loglow/TrueUp-Glide-Mod/STL/PSU Mount.stl

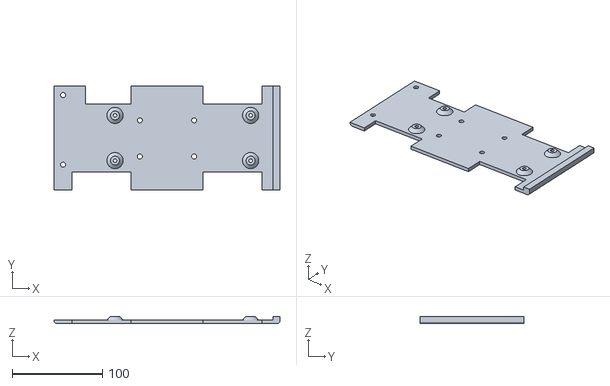
[picture p16: CAD file, 2017-04-15]
STL/PSU Mount.stl
250.0 x 115.0 x 8.00
