loglow/TrueUp-Glide-Mod/STL/Frame Foot.stl

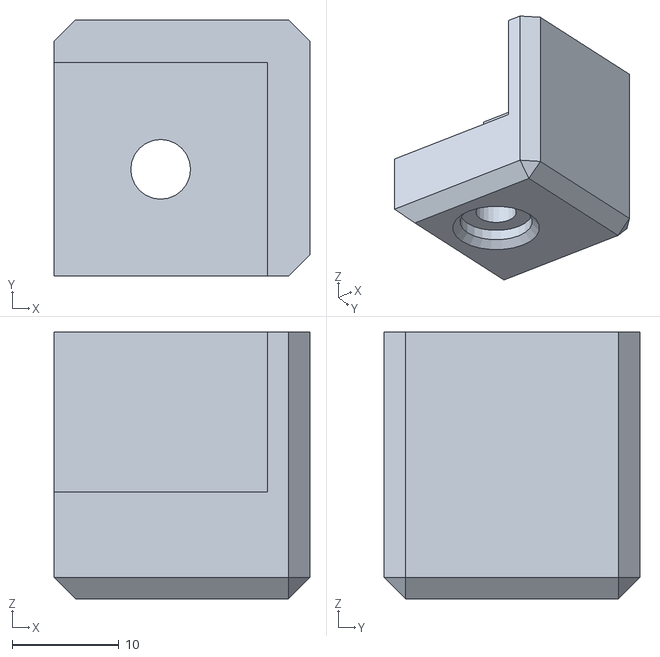
[picture p17: CAD file, 2017-04-15]
STL/Frame Foot.stl
24.0 x 24.0 x 25.0
