loglow/TrueUp-Glide-Mod/STL/MKS Mount.stl

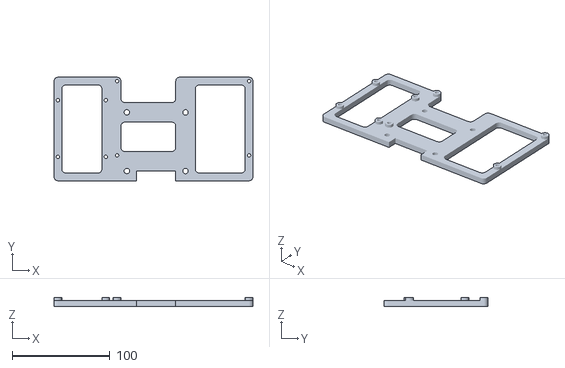
[picture p18: CAD file, 2017-04-15]
STL/MKS Mount.stl
203.5 x 106.0 x 9.00
