loglow/TrueUp-Glide-Mod/STL/Y Belt Keeper Spacer.stl

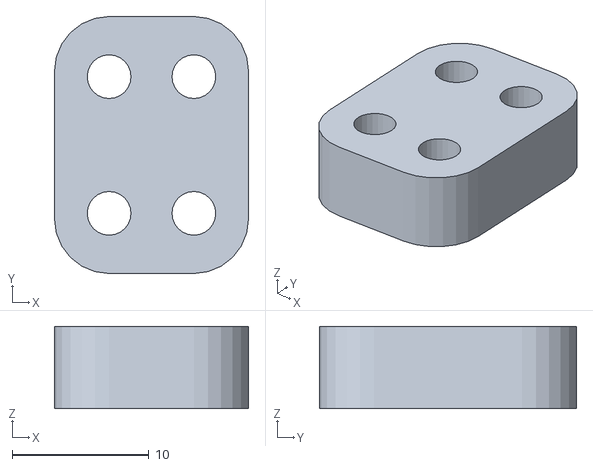
[picture p19: CAD file, 2017-04-15]
STL/Y Belt Keeper Spacer.stl
14.2 x 18.8 x 6.00
