loglow/TrueUp-Glide-Mod/STL/Z Glide Body, Left.stl

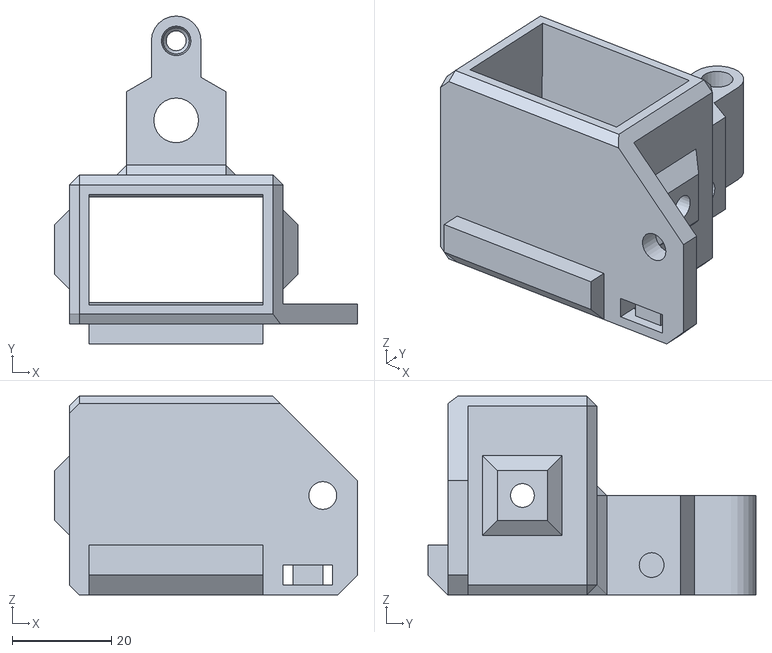
[picture p20: CAD file, 2017-04-15]
STL/Z Glide Body, Left.stl
61.0 x 66.0 x 40.0
