loglow/TrueUp-Glide-Mod/STL/Y Idler Bracket.stl

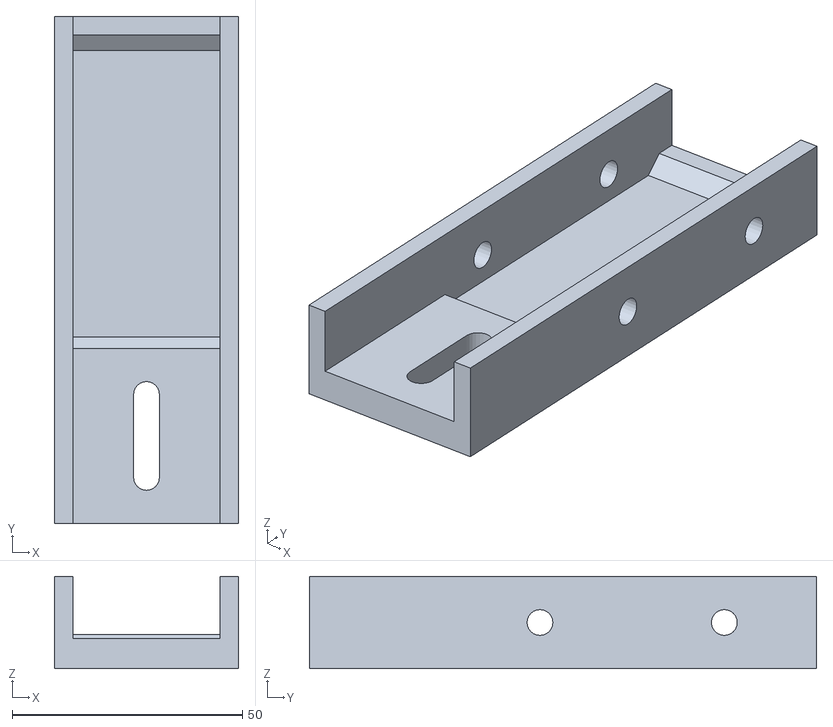
[picture p21: CAD file, 2017-04-15]
STL/Y Idler Bracket.stl
40.0 x 110.0 x 20.0
