loglow/TrueUp-Glide-Mod/STL/Y Belt Keeper Teeth.stl

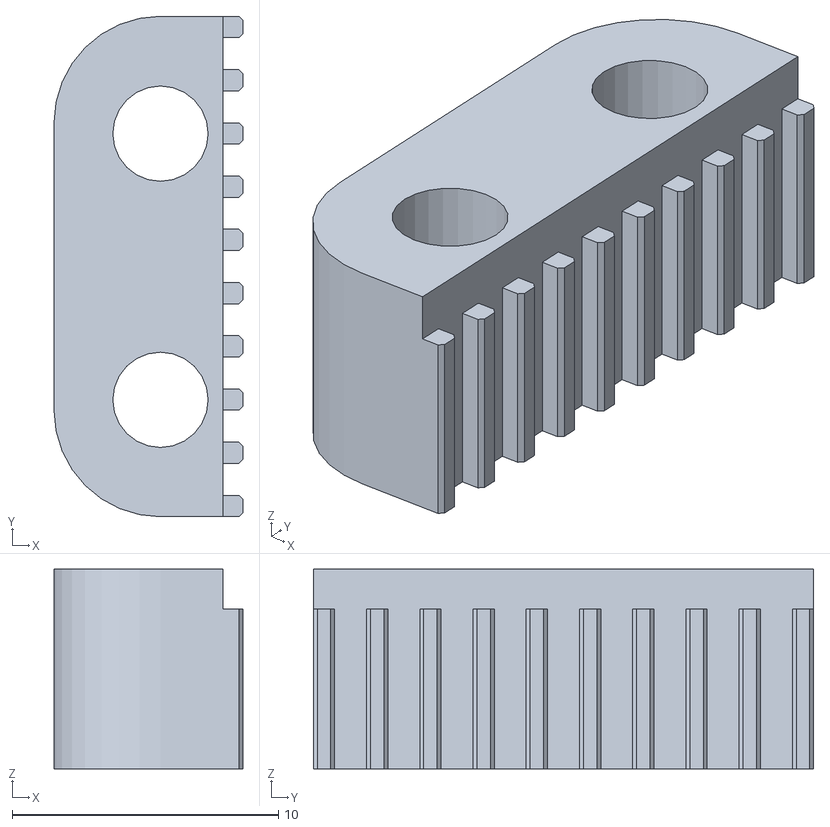
[picture p22: CAD file, 2017-04-15]
STL/Y Belt Keeper Teeth.stl
7.10 x 18.8 x 7.50
