loglow/TrueUp-Glide-Mod/STL/Handle.stl

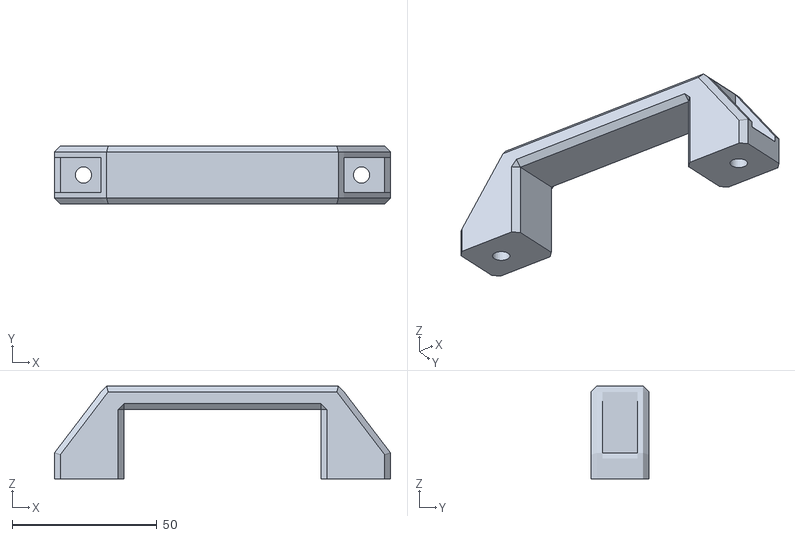
[picture p23: CAD file, 2017-04-15]
STL/Handle.stl
116.0 x 20.0 x 32.0
