loglow/TrueUp-Glide-Mod/STL/Control Box, Left.stl

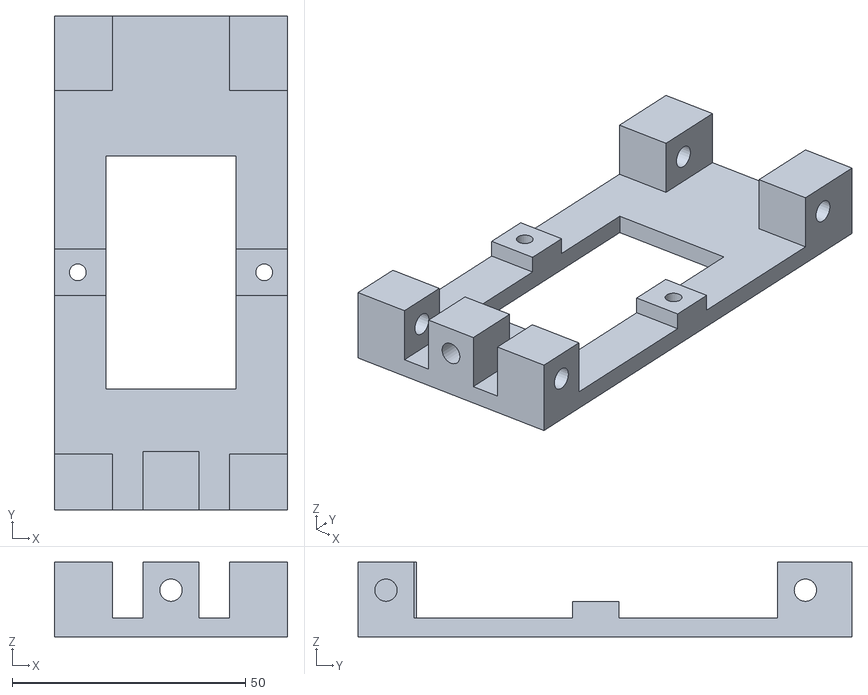
[picture p24: CAD file, 2017-04-15]
STL/Control Box, Left.stl
50.0 x 106.0 x 16.0
