loglow/TrueUp-Glide-Mod/STL/Y Mount Bracket.stl

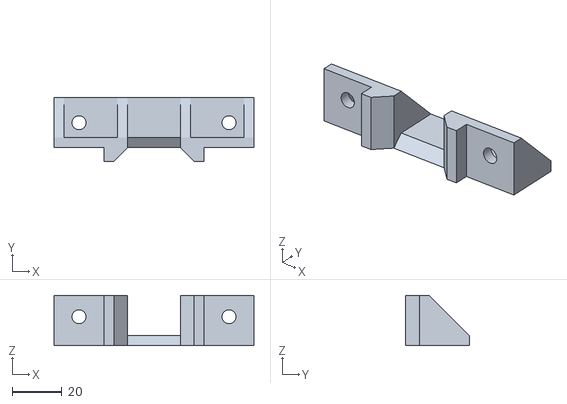
[picture p25: CAD file, 2017-04-15]
STL/Y Mount Bracket.stl
80.0 x 25.4 x 20.0
