loglow/TrueUp-Glide-Mod/STL/Y Belt Keeper Flat.stl

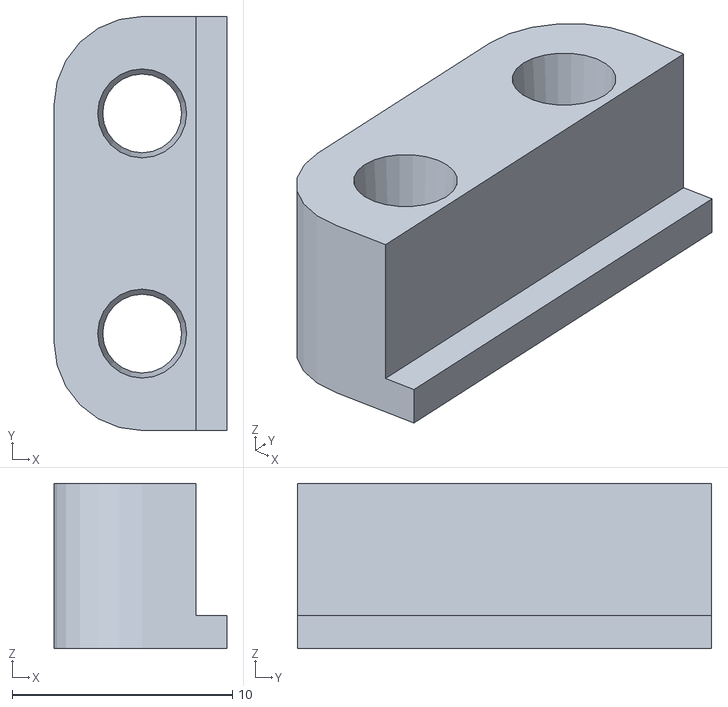
[picture p26: CAD file, 2017-04-15]
STL/Y Belt Keeper Flat.stl
7.85 x 18.8 x 7.50
