loglow/TrueUp-Glide-Mod/STL/Spool Mount.stl

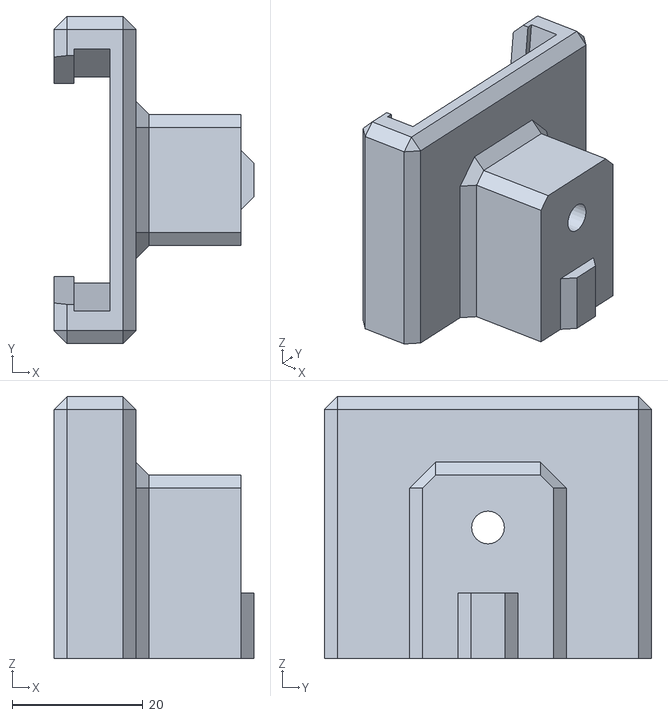
[picture p27: CAD file, 2017-04-15]
STL/Spool Mount.stl
30.5 x 50.0 x 40.0
