loglow/TrueUp-Glide-Mod/STL/Control Box, Bottom.stl

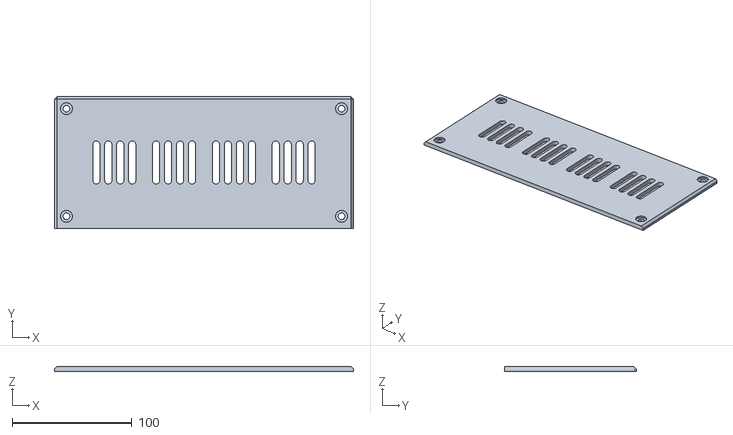
[picture p28: CAD file, 2017-04-15]
STL/Control Box, Bottom.stl
250.0 x 110.0 x 4.00
