loglow/TrueUp-Glide-Mod/STL/Top Corner, Left.stl

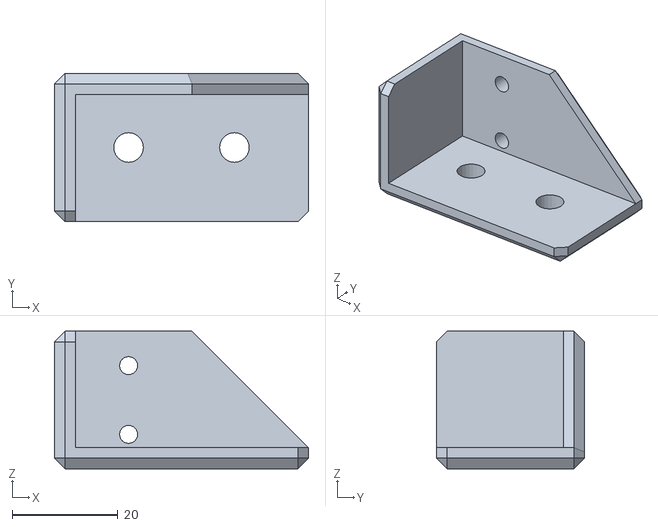
[picture p29: CAD file, 2017-04-15]
STL/Top Corner, Left.stl
48.0 x 28.0 x 26.0
