loglow/TrueUp-Glide-Mod/STL/Crossover Cover.stl

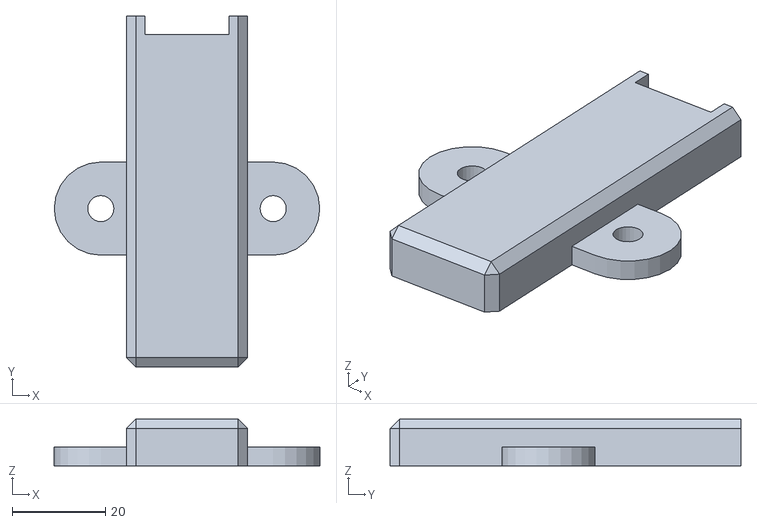
[picture p30: CAD file, 2017-04-15]
STL/Crossover Cover.stl
57.0 x 75.4 x 10.0
