loglow/TrueUp-Glide-Mod/STL/Z Endstop Bracket.stl

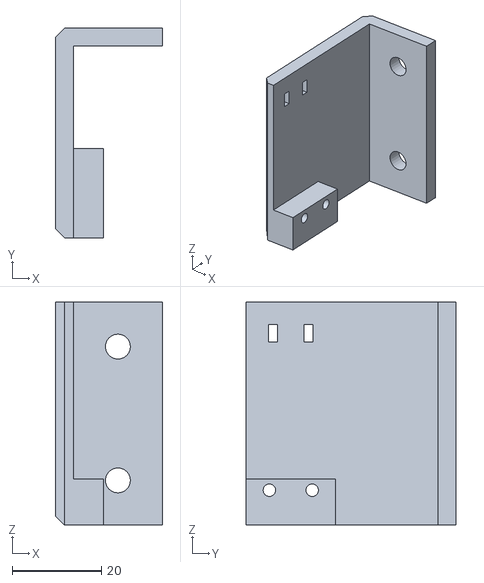
[picture p31: CAD file, 2017-04-15]
STL/Z Endstop Bracket.stl
24.0 x 47.0 x 50.0
