loglow/TrueUp-Glide-Mod/STL/X Motor Mount.stl

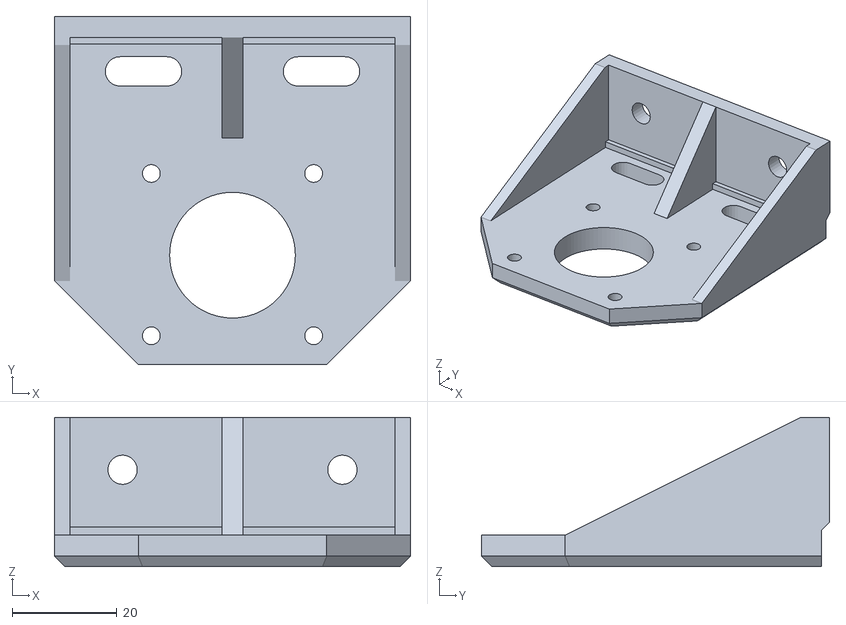
[picture p32: CAD file, 2017-04-15]
STL/X Motor Mount.stl
68.0 x 66.5 x 28.5
