loglow/TrueUp-Glide-Mod/STL/Print Fan Nozzle.stl

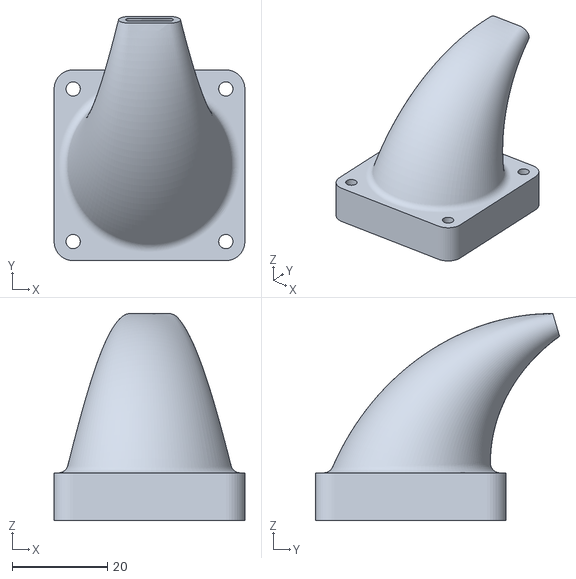
[picture p33: CAD file, 2017-04-15]
STL/Print Fan Nozzle.stl
40.0 x 51.2 x 43.4
