loglow/TrueUp-Glide-Mod/STL/Front Foot.stl

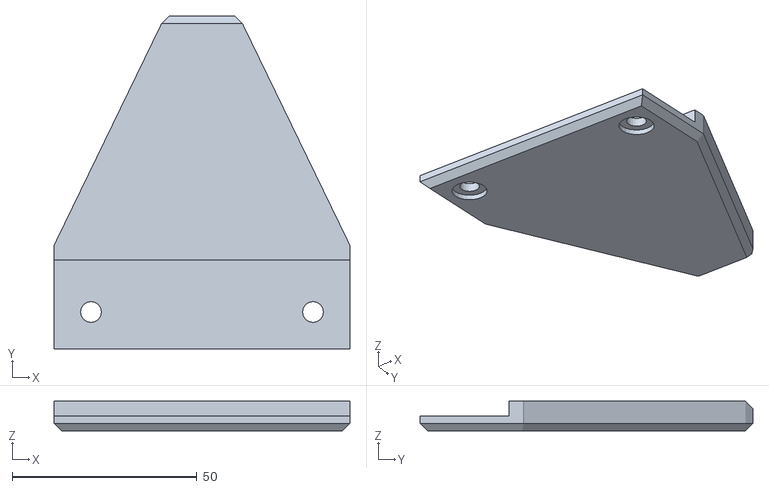
[picture p34: CAD file, 2017-04-15]
STL/Front Foot.stl
80.0 x 90.0 x 8.00
