loglow/TrueUp-Glide-Mod/STL/PSU Top.stl

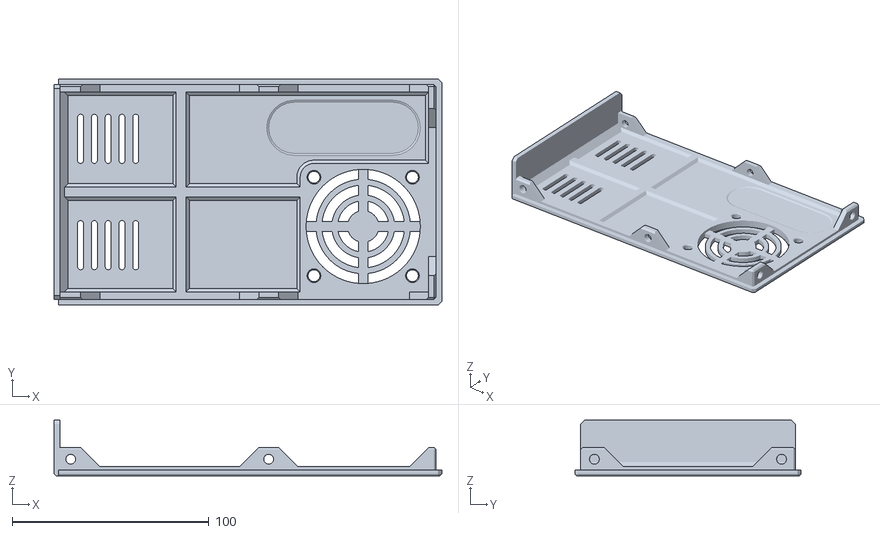
[picture p35: CAD file, 2017-04-15]
STL/PSU Top.stl
197.0 x 115.0 x 28.4
