loglow/TrueUp-Glide-Mod/STL/Control Box Fan Mount.stl

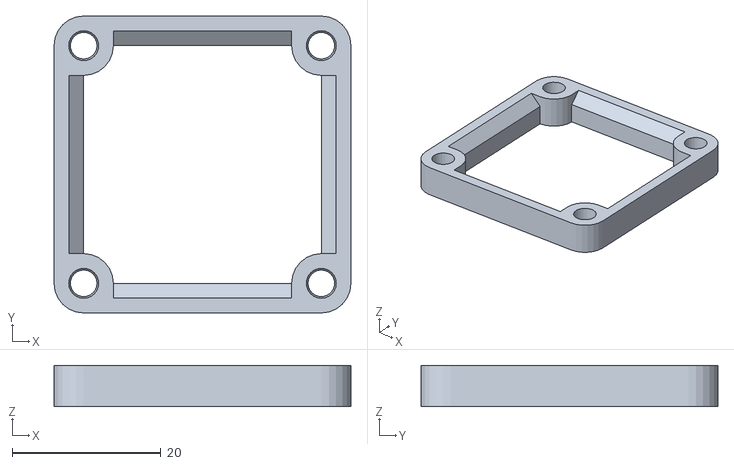
[picture p36: CAD file, 2017-04-15]
STL/Control Box Fan Mount.stl
40.0 x 40.0 x 5.56
