loglow/TrueUp-Glide-Mod/STL/Control Box, Front.stl

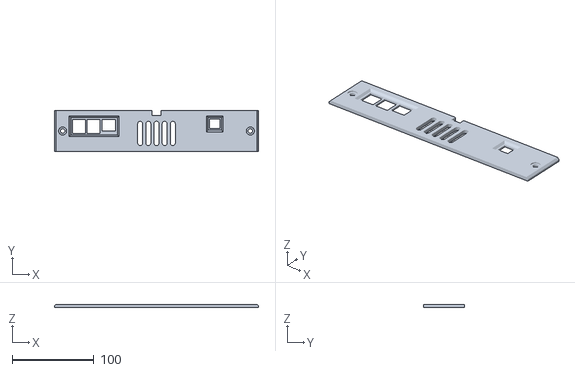
[picture p37: CAD file, 2017-04-15]
STL/Control Box, Front.stl
250.0 x 50.0 x 4.00
