loglow/TrueUp-Glide-Mod/STL/Z Bearing Mount.stl

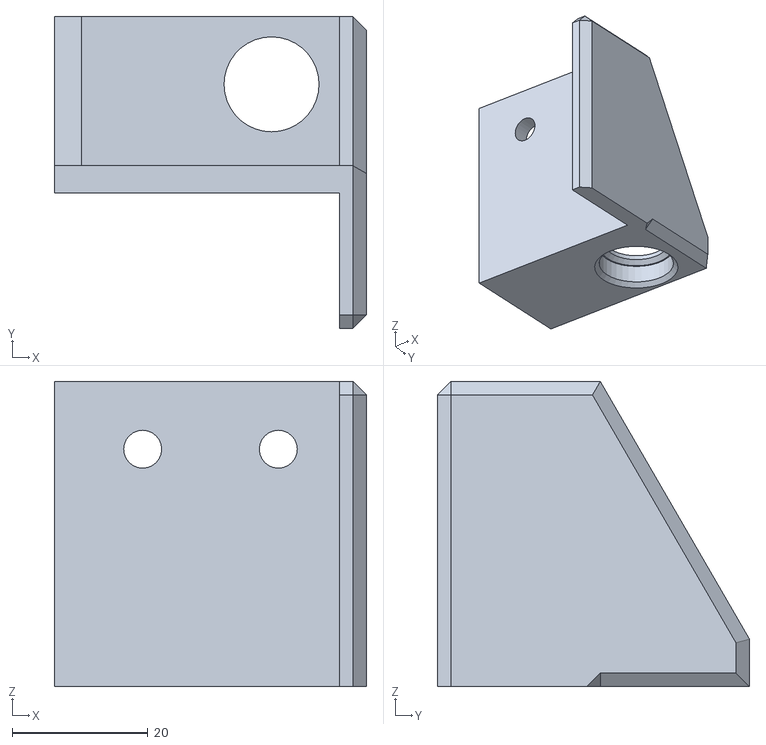
[picture p38: CAD file, 2017-04-15]
STL/Z Bearing Mount.stl
46.0 x 46.0 x 45.0
