loglow/TrueUp-Glide-Mod/STL/Spool Holder.stl

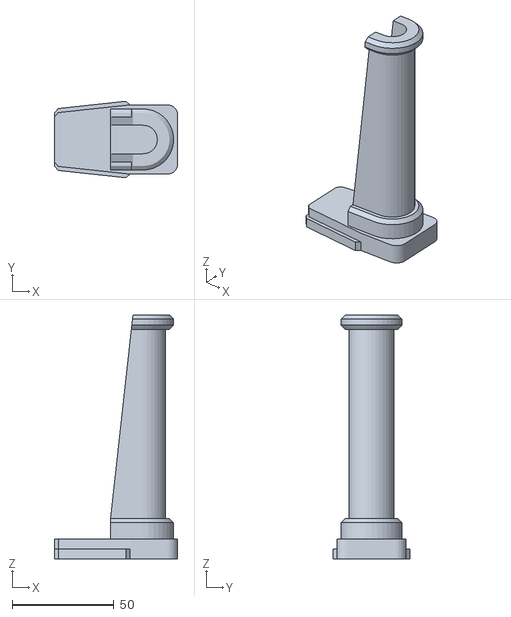
[picture p39: CAD file, 2017-04-15]
STL/Spool Holder.stl
60.6 x 37.6 x 119.8
