loglow/TrueUp-Glide-Mod/STL/X Leveling Jig.stl

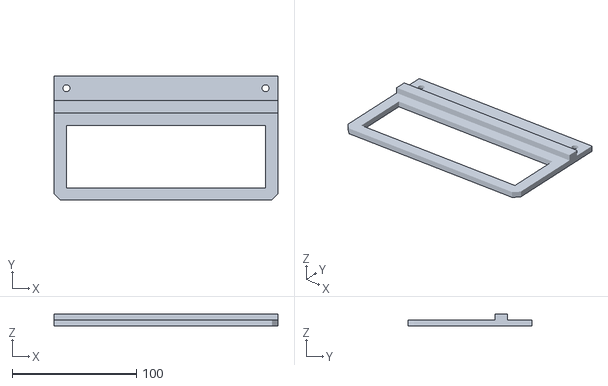
[picture p40: CAD file, 2017-04-15]
STL/X Leveling Jig.stl
180.0 x 100.0 x 10.0
