loglow/TrueUp-Glide-Mod/STL/Y Center.stl

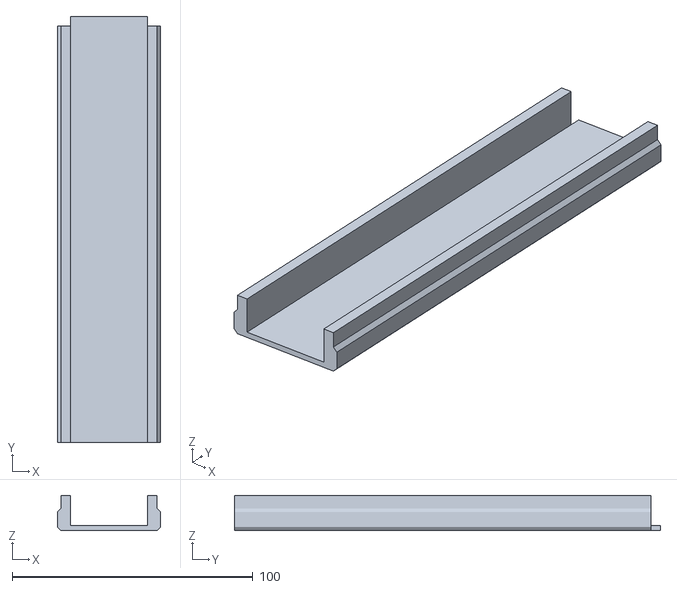
[picture p41: CAD file, 2017-04-15]
STL/Y Center.stl
42.9 x 177.0 x 14.6
