loglow/TrueUp-Glide-Mod/STL/Z Motor Mount.stl

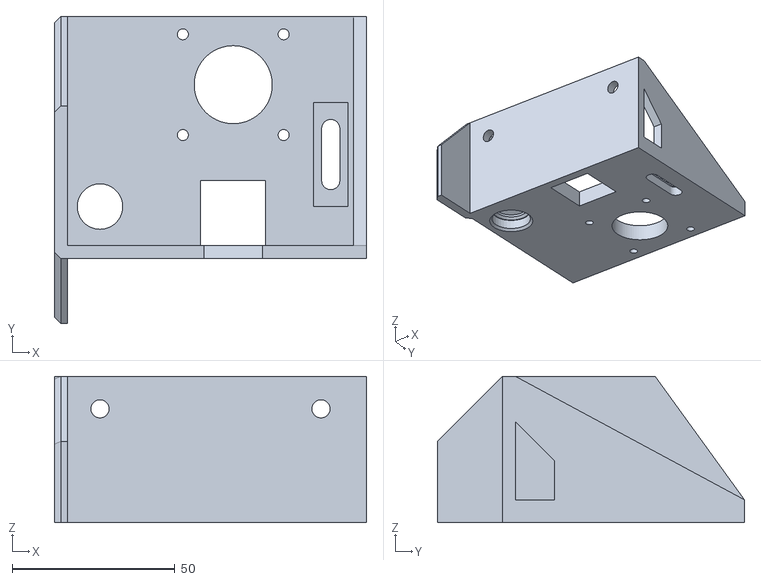
[picture p42: CAD file, 2017-04-15]
STL/Z Motor Mount.stl
96.0 x 94.5 x 45.0
