loglow/TrueUp-Glide-Mod/STL/Loom Cap.stl

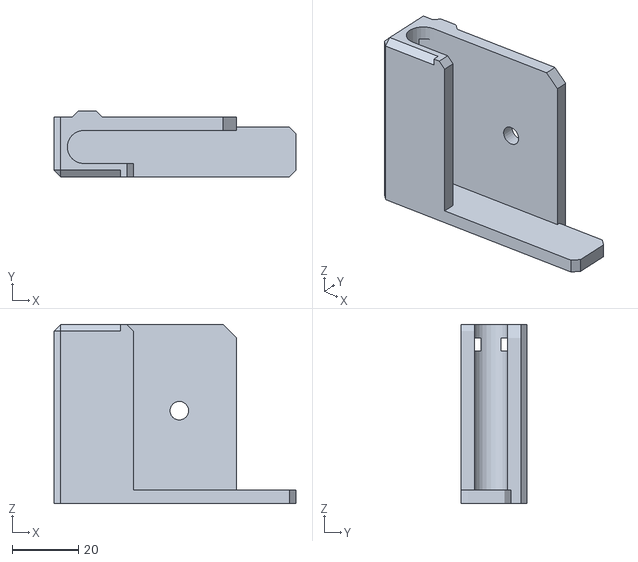
[picture p43: CAD file, 2017-04-15]
STL/Loom Cap.stl
73.0 x 19.8 x 54.0
