loglow/TrueUp-Glide-Mod/STL/Control Box, Top.stl

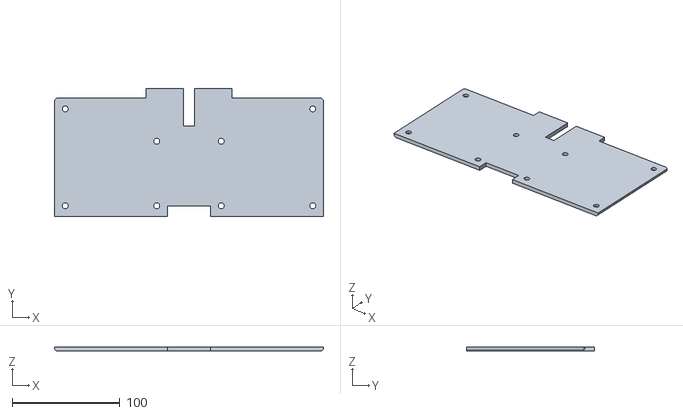
[picture p44: CAD file, 2017-04-15]
STL/Control Box, Top.stl
250.0 x 119.0 x 4.00
