loglow/TrueUp-Glide-Mod/STL/X Belt Keeper.stl

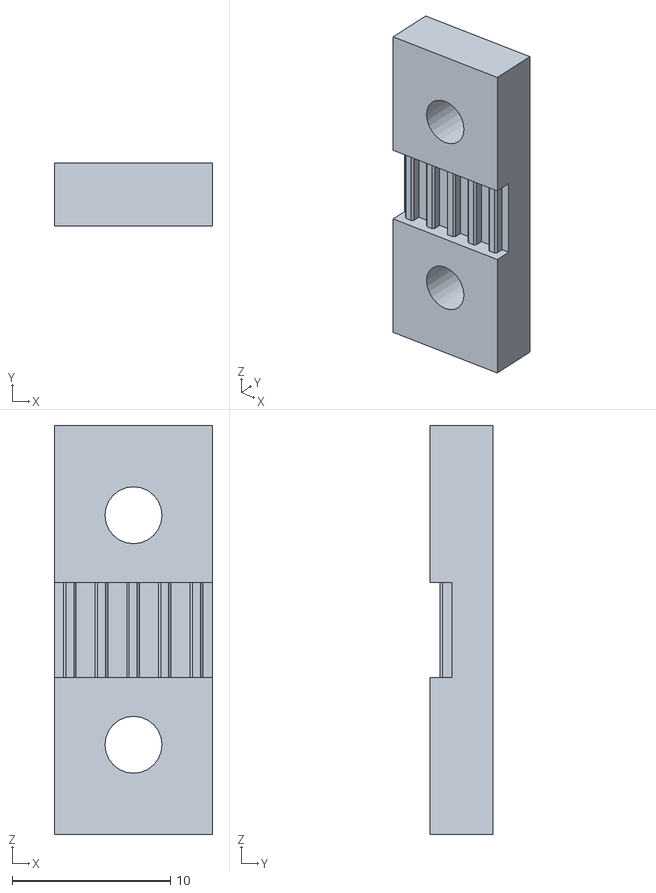
[picture p45: CAD file, 2017-04-15]
STL/X Belt Keeper.stl
10.0 x 4.00 x 25.8
