loglow/TrueUp-Glide-Mod/STL/Control Box, Right.stl

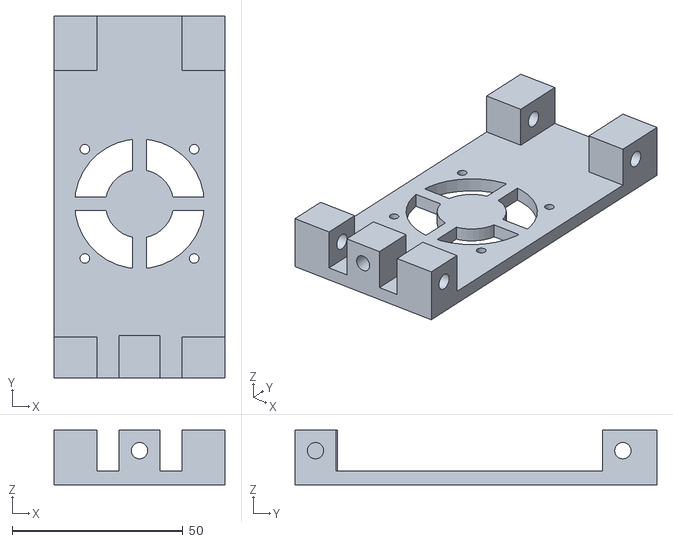
[picture p46: CAD file, 2017-04-15]
STL/Control Box, Right.stl
50.0 x 106.0 x 16.0
