loglow/TrueUp-Glide-Mod/STL/Print Fan Top.stl

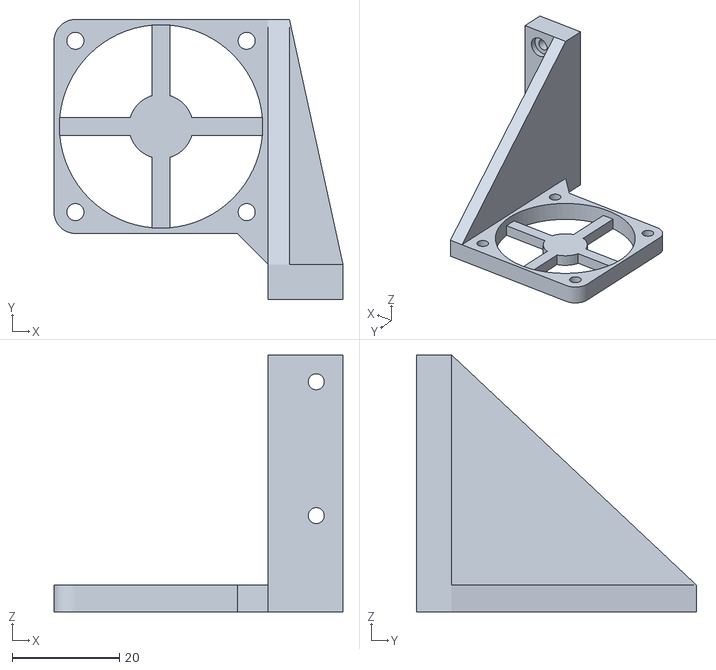
[picture p47: CAD file, 2017-04-15]
STL/Print Fan Top.stl
54.0 x 52.3 x 48.0
